TheSuperPixel/STM32_LVGL_Board/测试例程/使用cubeMX重要说明，必看！！！.jpg

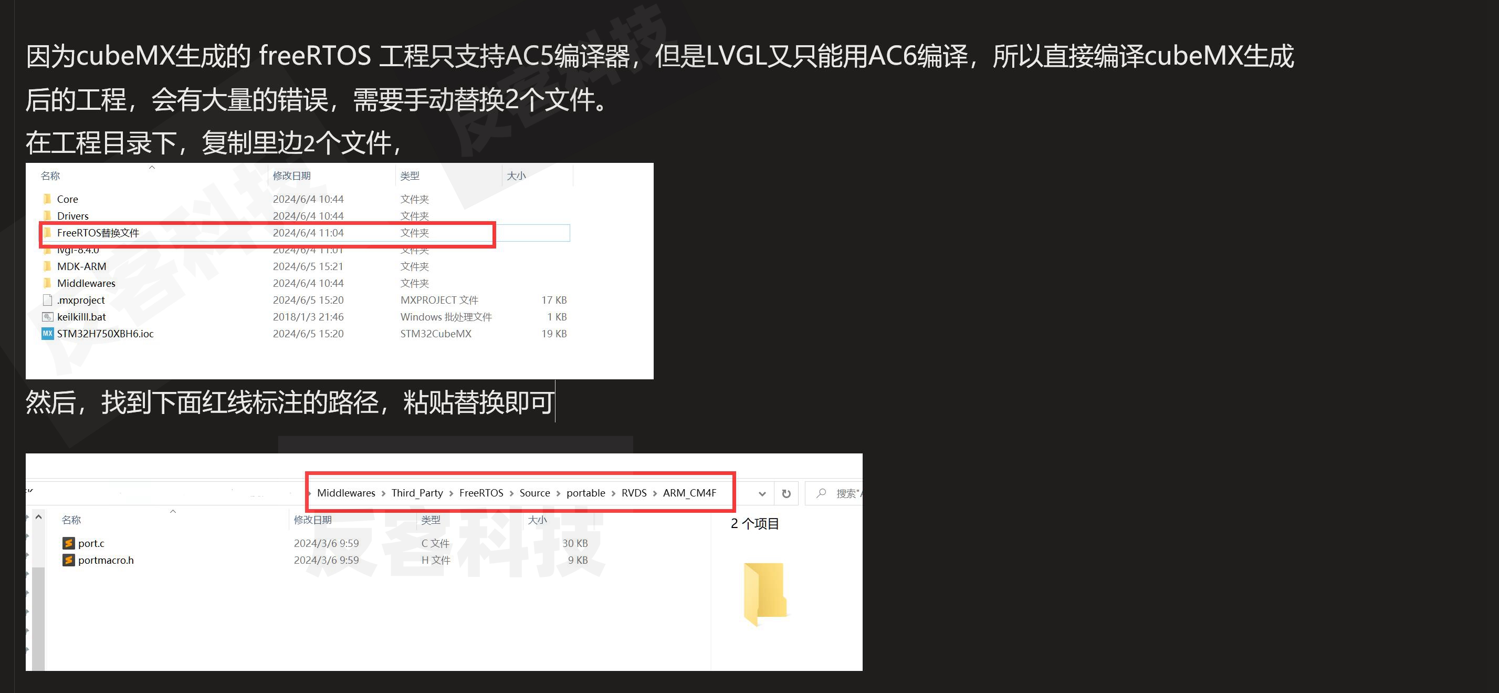
测试例程/使用cubeMX重要说明，必看！！！.jpg
