TheSuperPixel/STM32_LVGL_Board/测试例程/复制LVGL到SRAM - 修改说明1.png

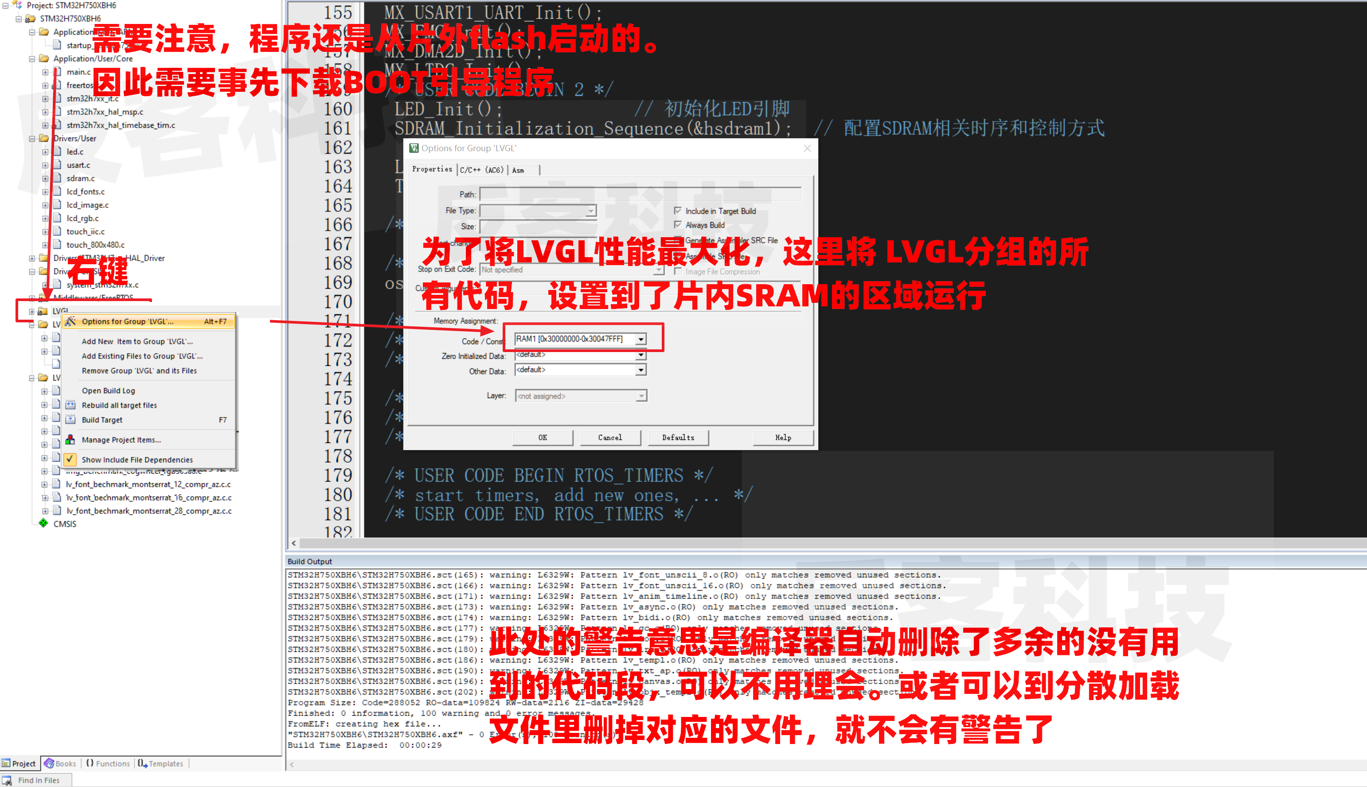
测试例程/复制LVGL到SRAM - 修改说明1.png
