TheSuperPixel/STM32_LVGL_Board/测试例程/重要说明！！！必看1.png

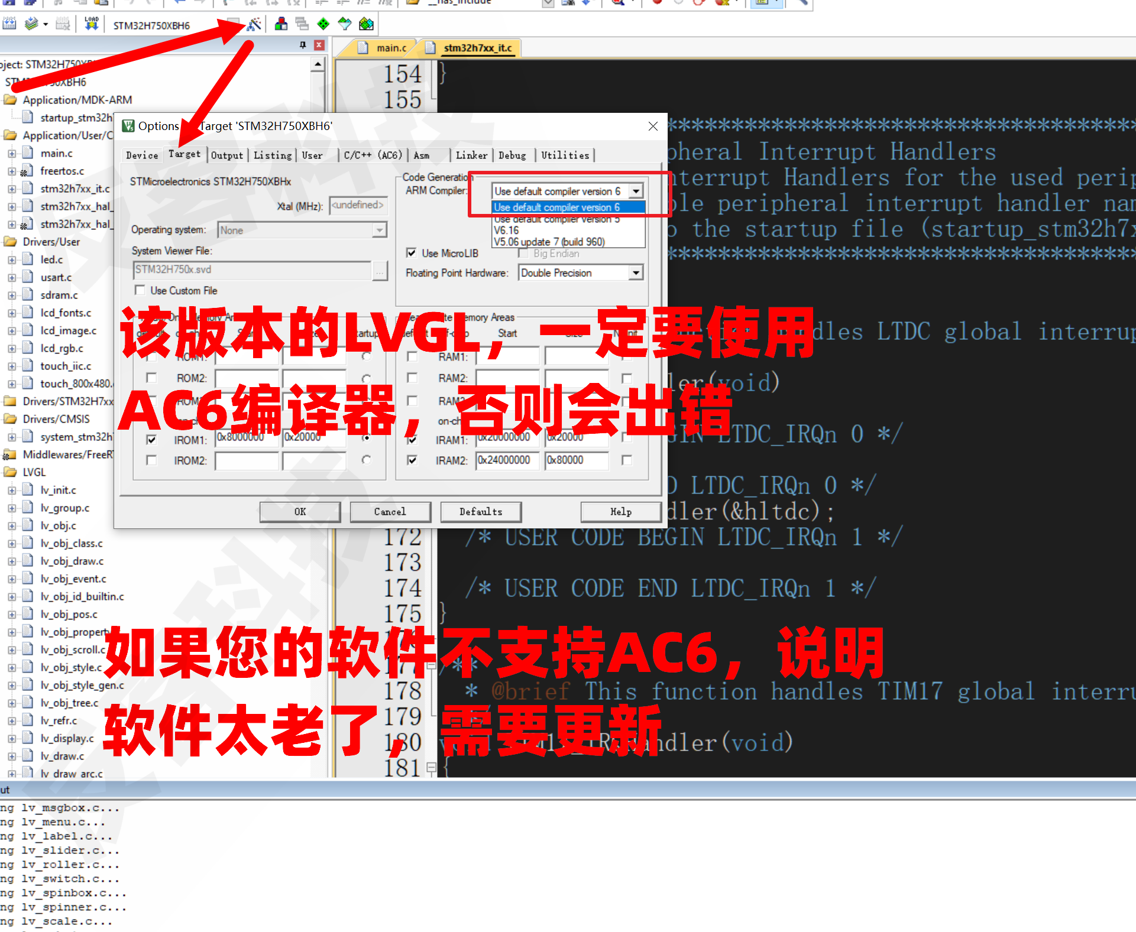
测试例程/重要说明！！！必看1.png
